elagil/loeti/hardware/simulation/switchmode.asc

C1: cap; 88µ; Rser=0.03
C2: cap; 40p; Rser=0
C3: cap; 100n
C4: cap; 10µ
D1: schottky; 1N5818
L1: ind; 6µ
L2: ind; 10µ
M1: pmos; Si4835DY
Q1: npn; BC817-40
Q2: pnp; BC807-40
Q3: npn; BC817-40
Q4: npn; BC817-40
R1: res; 1
R2: res; 3.2
R3: res; 1k
R4: res; 20m
R5: res; 1k
R6: res; 1k
R7: res; 5k
R8: res; 5k
R9: res; 100k
R10: res; 10k
R11: res; 100k
R12: res; 400
U1: OP492
U2: OP492
U3: OP492
V1: voltage; 20; Rser=0.5
V2: voltage; PULSE(0 3.3 0 0 0 2u 5.8u); Rser=10
Named nets: 0, sense+, sense-
.tran 0 5m 0m
