elagil/loeti/firmware/loeti/common/src/power.rs

//! Handles USB PD negotiation.
use crate::NEGOTIATED_SUPPLY_SIG;
use crate::app::UcpdResources;
use defmt::{Format, debug, warn};
use embassy_futures::select::{Either, select};
use embassy_stm32::gpio::Output;
use embassy_stm32::ucpd::{self, CcPhy, CcPull, CcSel, CcVState, PdPhy, Ucpd};
use embassy_stm32::{bind_interrupts, peripherals};
use embassy_time::{Duration, Timer, with_timeout};
use uom::si::{electric_current, electric_potential};
use usbpd::protocol_layer::message::data::request;
use usbpd::protocol_layer::message::data::source_capabilities::SourceCapabilities;
use usbpd::sink::device_policy_manager::DevicePolicyManager;
use usbpd::sink::policy_engine::Sink;
use usbpd::timers::Timer as SinkTimer;
use usbpd_traits::Driver as SinkDriver;

use {defmt_rtt as _, panic_probe as _};

bind_interrupts!(struct Irqs {
    UCPD1 => ucpd::InterruptHandler<peripherals::UCPD1>;
});

#[derive(Debug, Format)]
#[allow(clippy::missing_docs_in_private_items)]
enum CableOrientation {
    Normal,
    Flipped,
    DebugAccessoryMode,
}

/// The sink driver.
struct UcpdSinkDriver<'d> {
    /// The UCPD PD phy instance.
    pd_phy: PdPhy<'d, peripherals::UCPD1>,
}

impl<'d> UcpdSinkDriver<'d> {
    /// Create a new sink driver.
    fn new(pd_phy: PdPhy<'d, peripherals::UCPD1>) -> Self {
        Self { pd_phy }
    }
}

impl SinkDriver for UcpdSinkDriver<'_> {
    async fn wait_for_vbus(&mut self) {
        // The sink policy engine is only running when attached. Therefore VBus is present.
    }

    async fn receive(&mut self, buffer: &mut [u8]) -> Result<usize, usbpd_traits::DriverRxError> {
        self.pd_phy.receive(buffer).await.map_err(|err| match err {
            ucpd::RxError::Crc | ucpd::RxError::Overrun => usbpd_traits::DriverRxError::Discarded,
            ucpd::RxError::HardReset => usbpd_traits::DriverRxError::HardReset,
        })
    }

    async fn transmit(&mut self, data: &[u8]) -> Result<(), usbpd_traits::DriverTxError> {
        self.pd_phy.transmit(data).await.map_err(|err| match err {
            ucpd::TxError::Discarded => usbpd_traits::DriverTxError::Discarded,
            ucpd::TxError::HardReset => usbpd_traits::DriverTxError::HardReset,
        })
    }

    async fn transmit_hard_reset(&mut self) -> Result<(), usbpd_traits::DriverTxError> {
        self.pd_phy
            .transmit_hardreset()
            .await
            .map_err(|err| match err {
                ucpd::TxError::Discarded => usbpd_traits::DriverTxError::Discarded,
                ucpd::TxError::HardReset => usbpd_traits::DriverTxError::HardReset,
            })
    }
}

/// Waits until the cable was detached.
async fn wait_detached<T: ucpd::Instance>(cc_phy: &mut CcPhy<'_, T>) {
    loop {
        let (cc1, cc2) = cc_phy.vstate();
        if cc1 == CcVState::LOWEST && cc2 == CcVState::LOWEST {
            return;
        }
        cc_phy.wait_for_vstate_change().await;
    }
}

/// Waits until the cable was attached.
async fn wait_attached<T: ucpd::Instance>(cc_phy: &mut CcPhy<'_, T>) -> CableOrientation {
    loop {
        let (cc1, cc2) = cc_phy.vstate();
        if cc1 == CcVState::LOWEST && cc2 == CcVState::LOWEST {
            // Detached, wait until attached by monitoring the CC lines.
            cc_phy.wait_for_vstate_change().await;
            continue;
        }

        // Attached, wait for CC lines to be stable for tCCDebounce (100..200ms).
        if with_timeout(Duration::from_millis(100), cc_phy.wait_for_vstate_change())
            .await
            .is_ok()
        {
            // State has changed, restart detection procedure.
            continue;
        };

        // State was stable for the complete debounce period, check orientation.
        return match (cc1, cc2) {
            (_, CcVState::LOWEST) => CableOrientation::Normal, // CC1 connected
            (CcVState::LOWEST, _) => CableOrientation::Flipped, // CC2 connected
            _ => CableOrientation::DebugAccessoryMode,         // Both connected (special cable)
        };
    }
}

/// Timer implementation for usbpd.
struct EmbassySinkTimer {}

impl SinkTimer for EmbassySinkTimer {
    async fn after_millis(milliseconds: u64) {
        Timer::after_millis(milliseconds).await
    }
}

/// This device.
struct Device {
    /// The requested/negotiated potential in mV.
    negotiated_potential_mv: Option<u32>,
}

impl DevicePolicyManager for Device {
    async fn request(&mut self, source_capabilities: &SourceCapabilities) -> request::PowerSource {
        let supply = request::PowerSource::find_highest_fixed_voltage(source_capabilities).unwrap();
        self.negotiated_potential_mv =
            Some(supply.0.voltage().get::<electric_potential::millivolt>());

        request::PowerSource::new_fixed_specific(supply, request::CurrentRequest::Highest).unwrap()
    }

    /// Notify the device that it shall transition to a new power level.
    ///
    /// The device is informed about the request that was accepted by the source.
    async fn transition_power(&mut self, accepted: &request::PowerSource) {
        if let request::PowerSource::FixedVariableSupply(supply) = accepted {
            NEGOTIATED_SUPPLY_SIG.signal((
                self.negotiated_potential_mv.unwrap(),
                supply
                    .max_operating_current()
                    .get::<electric_current::milliampere>(),
            ))
        }
    }
}

/// Handle USB PD negotiation.
#[embassy_executor::task]
pub async fn ucpd_task(mut ucpd_resources: UcpdResources, mut ndb_pin: Output<'static>) {
    loop {
        let mut ucpd = Ucpd::new(
            ucpd_resources.ucpd.reborrow(),
            Irqs {},
            ucpd_resources.pin_cc1.reborrow(),
            ucpd_resources.pin_cc2.reborrow(),
            Default::default(),
        );

        ucpd.cc_phy().set_pull(CcPull::Sink);
        ndb_pin.set_high();

        debug!("Waiting for USB connection");
        let cable_orientation = wait_attached(ucpd.cc_phy()).await;
        debug!("USB cable attached, orientation: {}", cable_orientation);

        let cc_sel = match cable_orientation {
            CableOrientation::Normal => {
                debug!("Starting PD communication on CC1 pin");
                CcSel::CC1
            }
            CableOrientation::Flipped => {
                debug!("Starting PD communication on CC2 pin");
                CcSel::CC2
            }
            CableOrientation::DebugAccessoryMode => panic!("No PD communication in DAM"),
        };
        let (mut cc_phy, pd_phy) = ucpd.split_pd_phy(
            ucpd_resources.rx_dma.reborrow(),
            ucpd_resources.tx_dma.reborrow(),
            cc_sel,
        );

        let driver = UcpdSinkDriver::new(pd_phy);
        let mut sink: Sink<UcpdSinkDriver<'_>, EmbassySinkTimer, _> = Sink::new(
            driver,
            Device {
                negotiated_potential_mv: None,
            },
        );
        debug!("Run sink");

        match select(sink.run(), wait_detached(&mut cc_phy)).await {
            Either::First(result) => warn!("Sink loop broken with result: {}", result),
            Either::Second(_) => {
                debug!("Detached");
                continue;
            }
        }
    }
}
